vk5ln/1541-II_1581_power_distribution_pcb/images/IMG_20221224_080914.jpg

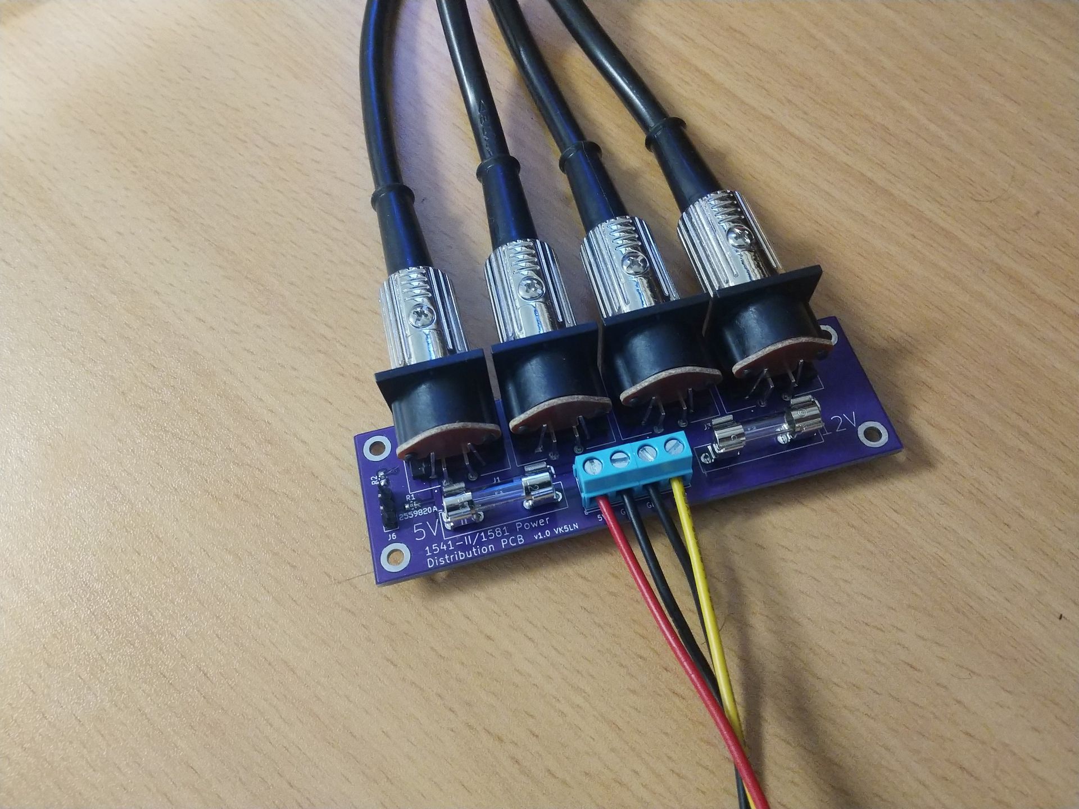
images/IMG_20221224_080914.jpg
