vk5ln/1541-II_1581_power_distribution_pcb/images/P1030955-1920.jpg

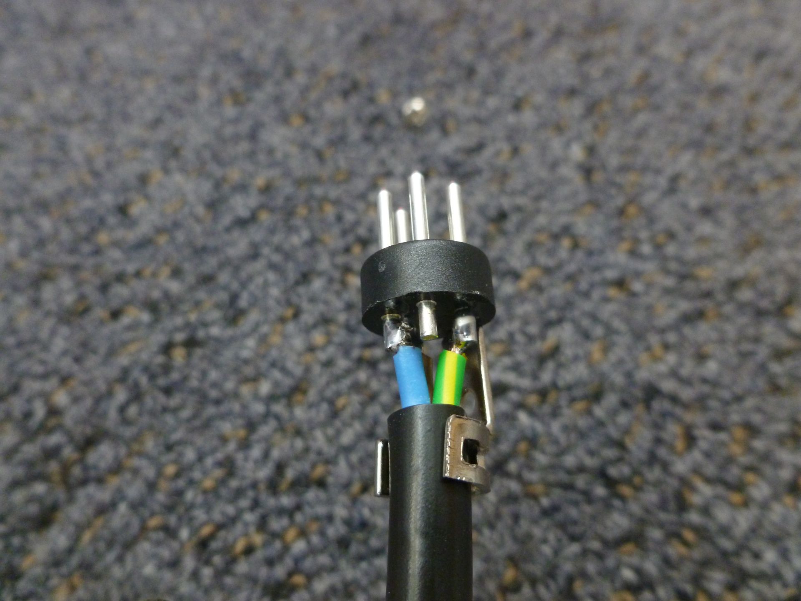
images/P1030955-1920.jpg
