vk5ln/1541-II_1581_power_distribution_pcb/kicad/1541-II PS.kicad_sch

## KiCad design kicad/1541-II PS.kicad_sch (2022-12-26)

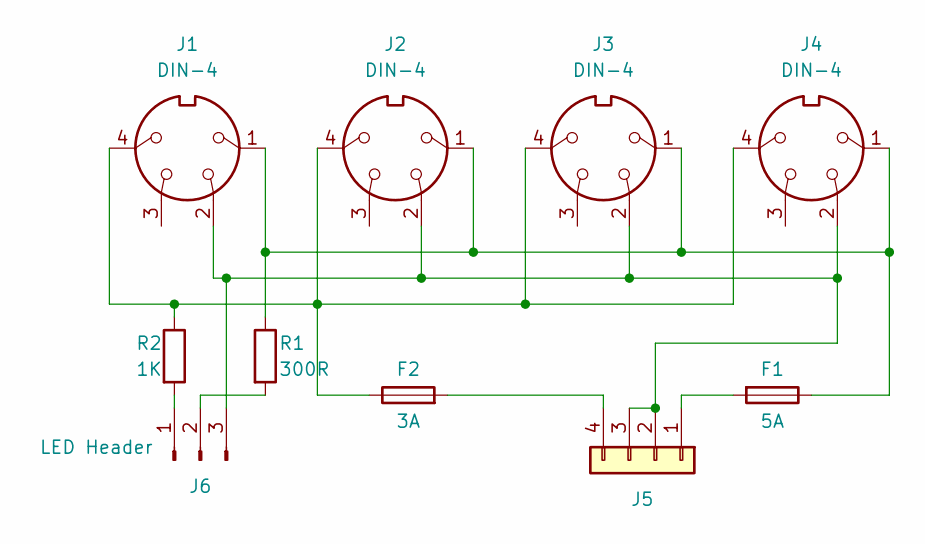
[picture p15: schematic 1541-II PS.kicad_sch]

Parts:
F1: 5A
F2: 3A
J1, J2, J3, J4: DIN-4
J5: Conn_01x04
J6: LED Header
R1: 300R
R2: 1K

Connections:
unnamed: F1.1, J1.1, J2.1, J3.1, J4.1, R1.1
unnamed: F1.2, J5.1
unnamed: F2.1, J1.4, J2.4, J3.4, J4.4, R2.1
unnamed: F2.2, J5.4
unnamed: J1.2, J2.2, J3.2, J4.2, J5.2, J5.3, J6.3
unnamed: J6.1, R2.2
unnamed: J6.2, R1.2
